wytr/KiCadCo2/Board2Pdf/temp/ESP8266_12F_BASIC-Edge_Cuts-colored.pdf

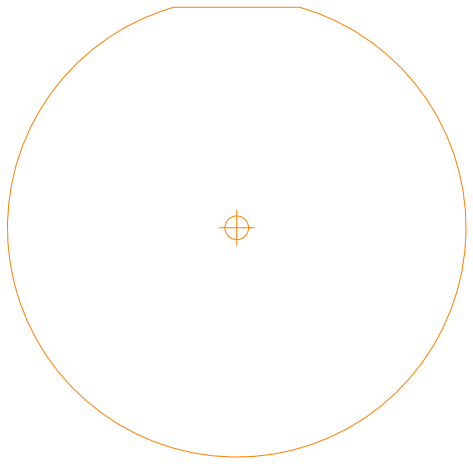
[picture p2: figure]
