wytr/KiCadCo2/Board2Pdf/temp/ESP8266_12F_BASIC-F_Silkscreen.pdf

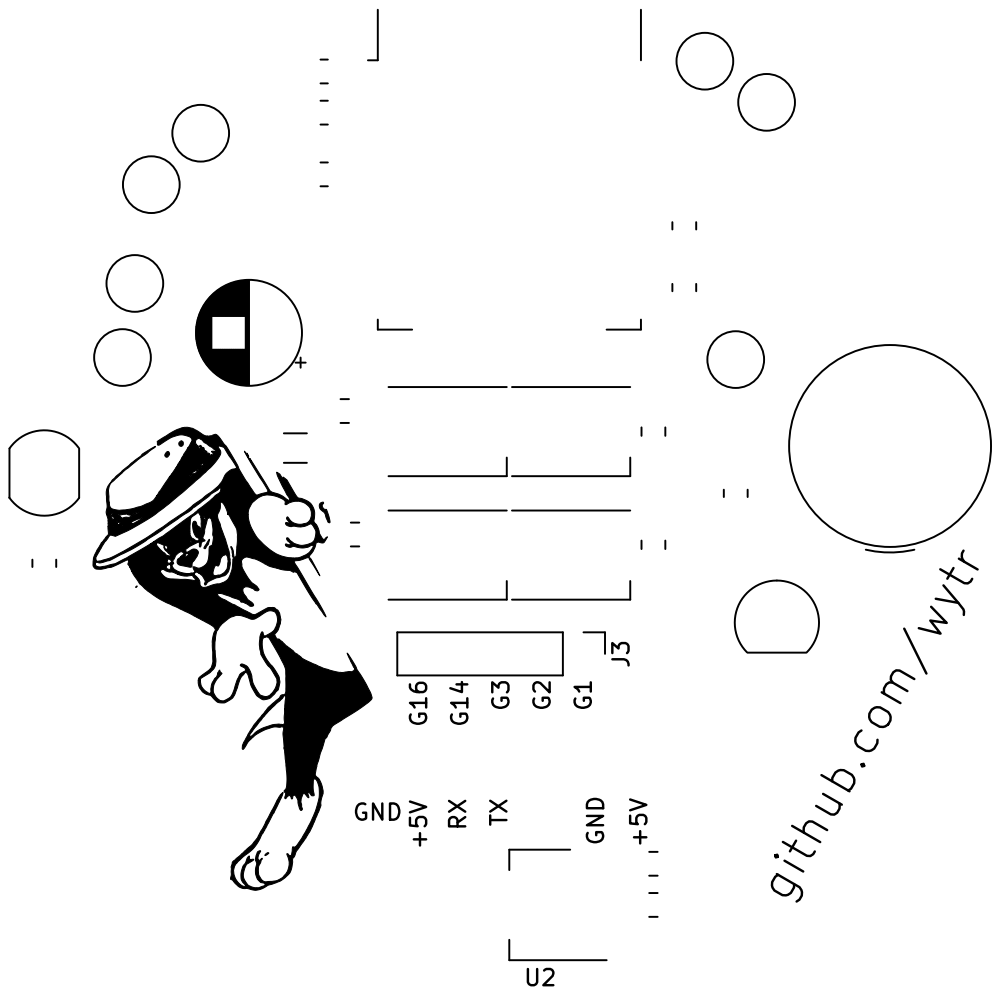
[picture p10: page 1]

G1 RXTX G3 G2 G14 GND github.com/wytr +5V G16 +5V GND
