wytr/KiCadCo2/Board2Pdf/temp/ESP8266_12F_BASIC-Edge_Cuts.pdf

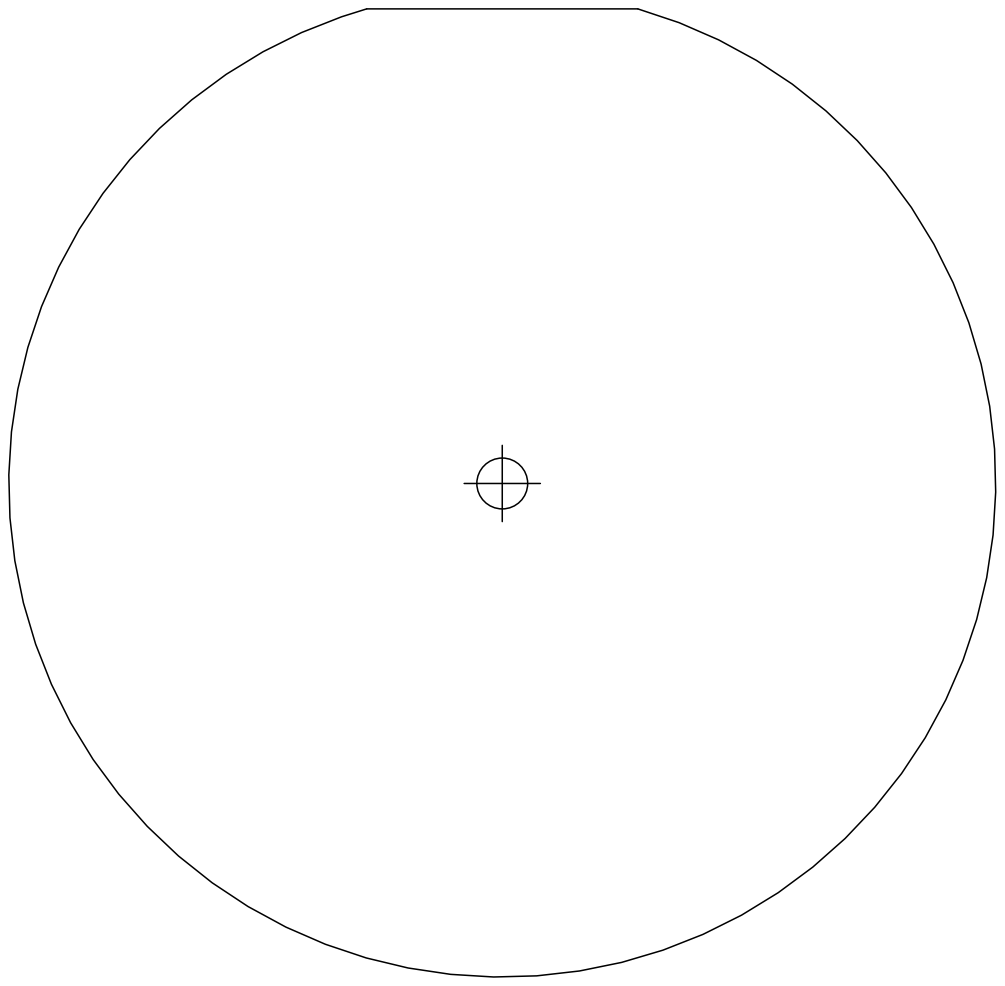
[picture p15: page 1]
