wytr/KiCadCo2/Board2Pdf/temp/ESP8266_12F_BASIC-F_Cu-colored.pdf

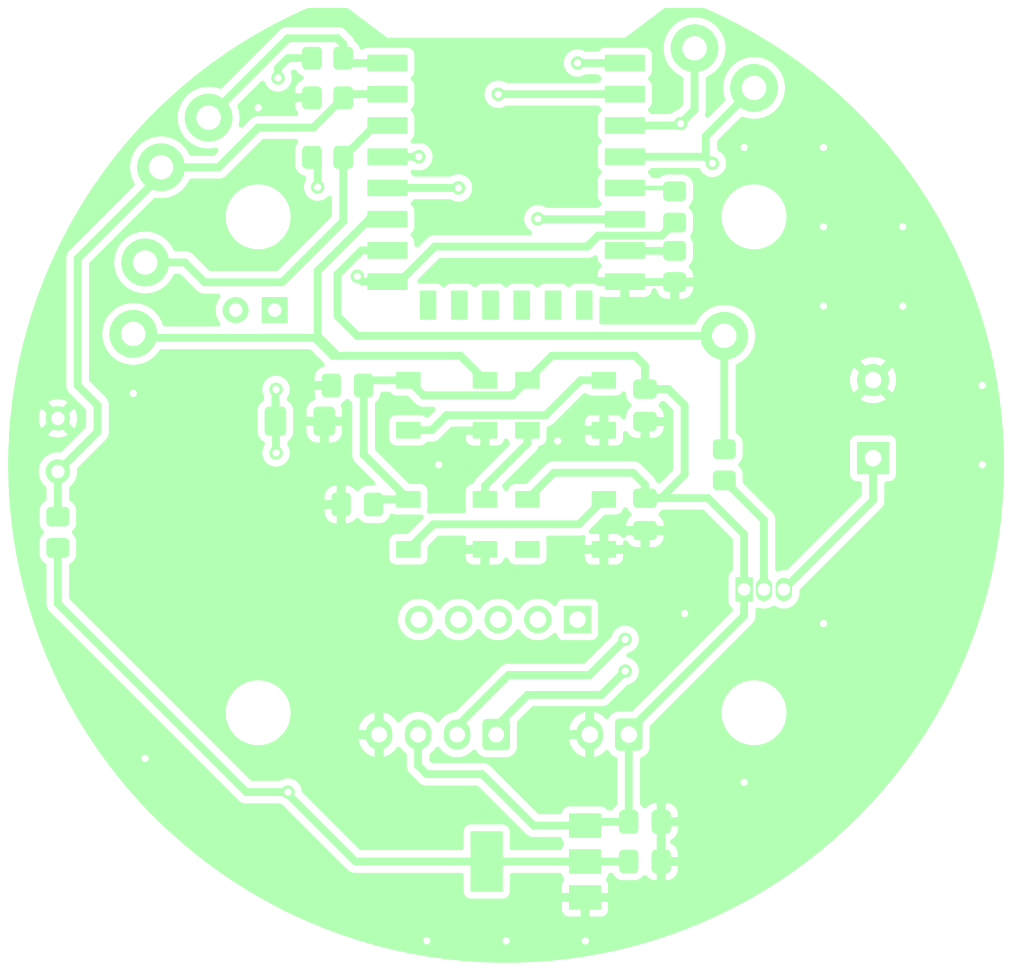
[picture p16: page 1]
