wytr/KiCadCo2/Board2Pdf/temp/ESP8266_12F_BASIC-F_Cu.pdf

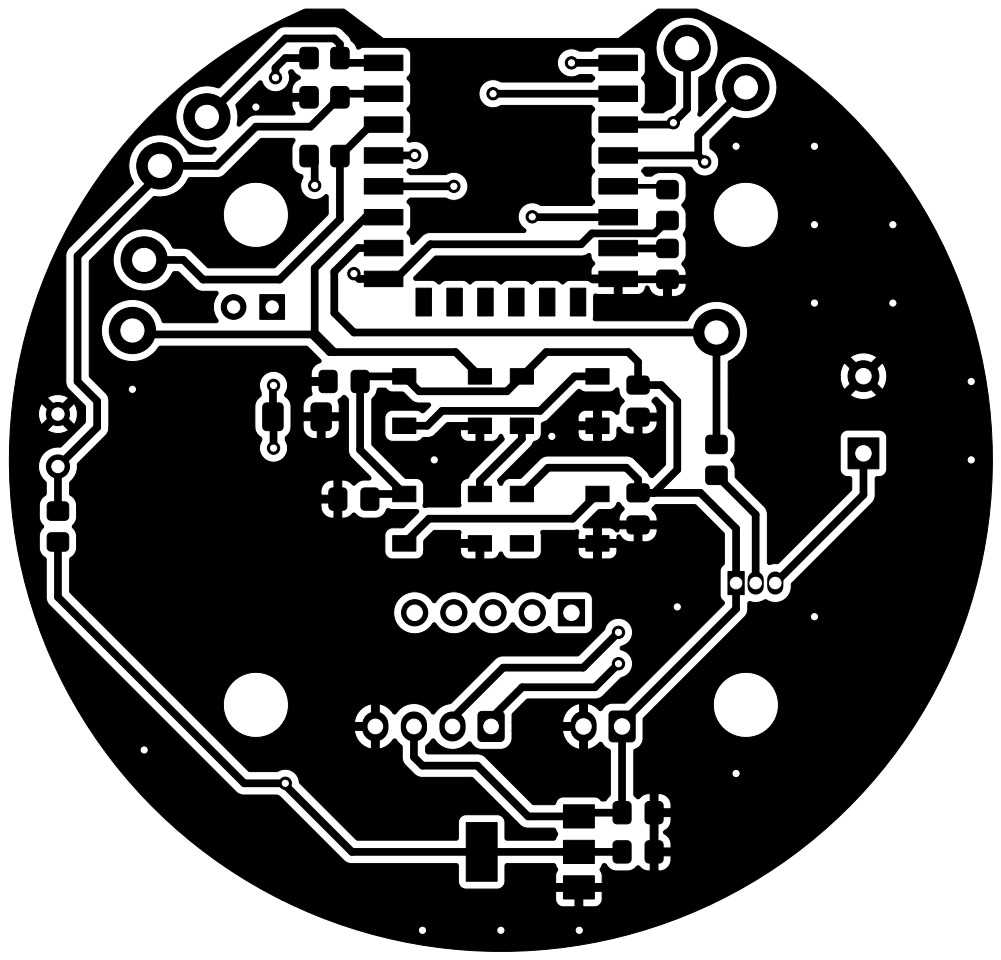
[picture p17: page 1]
