wytr/KiCadCo2/Board2Pdf/temp/ESP8266_12F_BASIC-F_Fab-colored.pdf

1 | 2 | 3 | 4 | 5 | 6

A

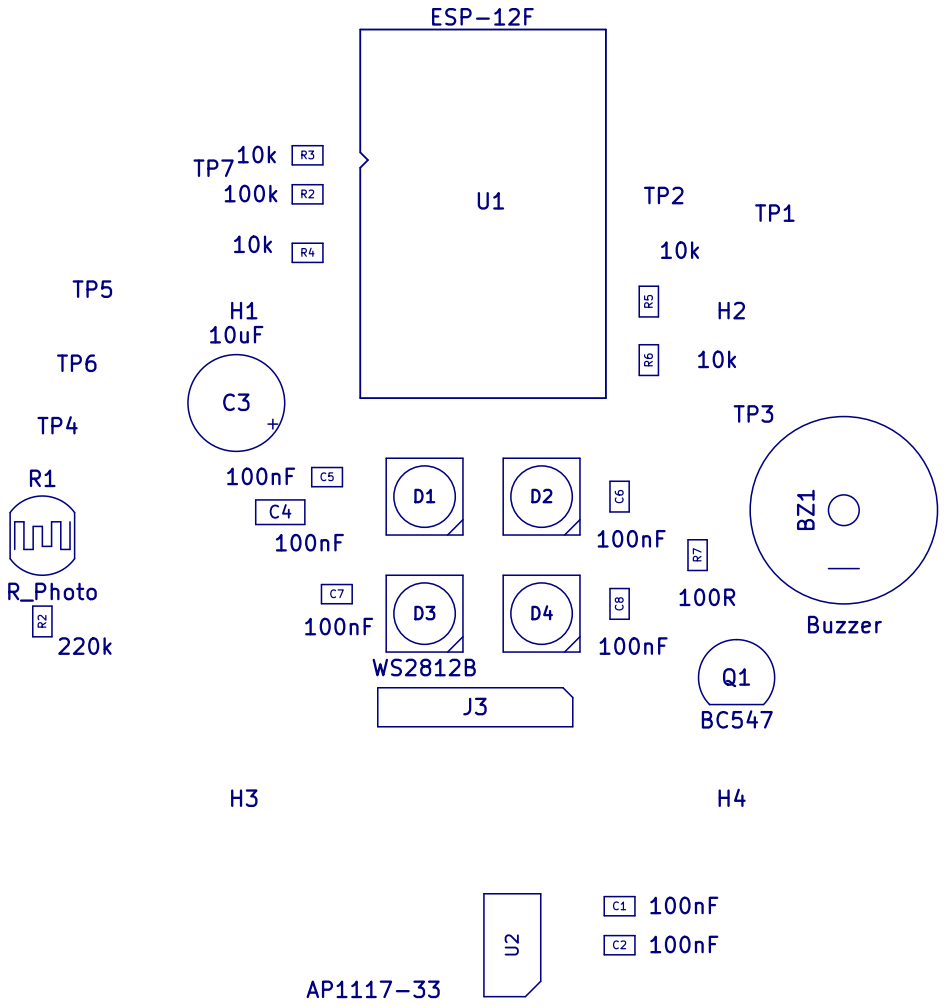
[picture p18: page 1]
