wytr/KiCadCo2/Board2Pdf/temp/ESP8266_12F_BASIC-F_Fab.pdf

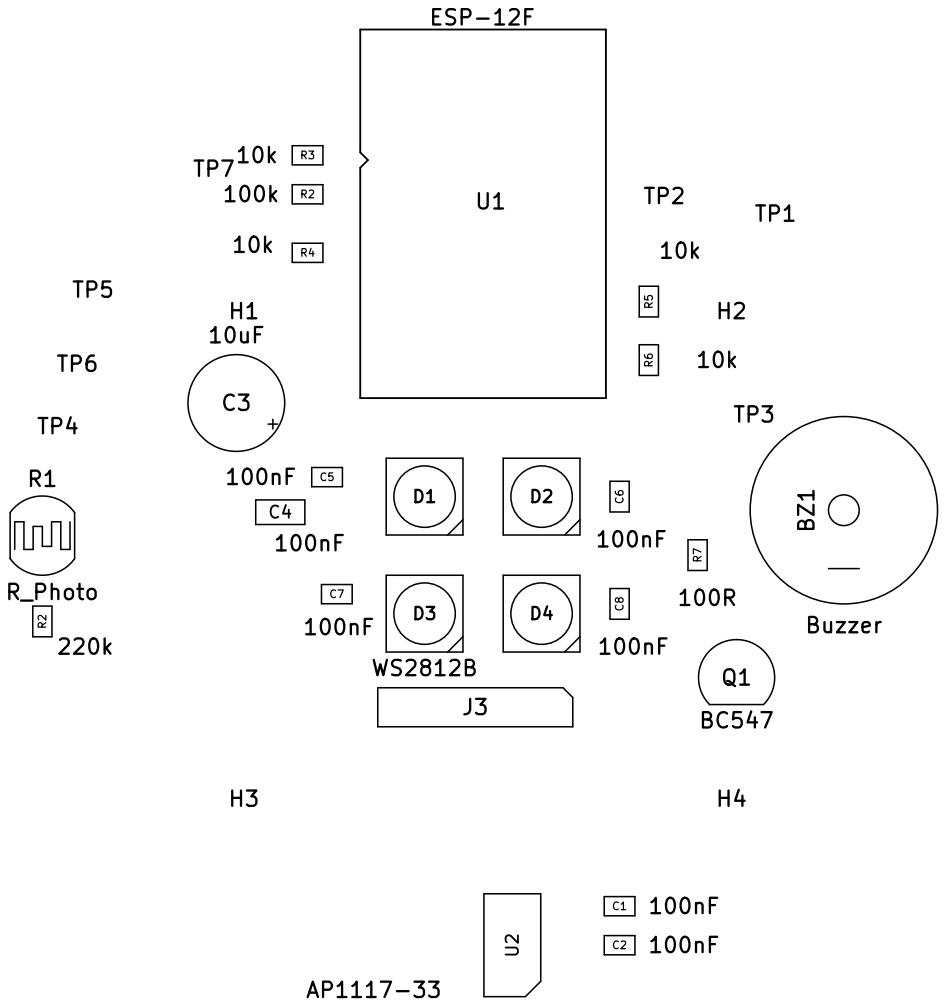
[picture p19: page 1]
