wytr/KiCadCo2/Board2Pdf/temp/ESP8266_12F_BASIC-F_Paste-colored.pdf

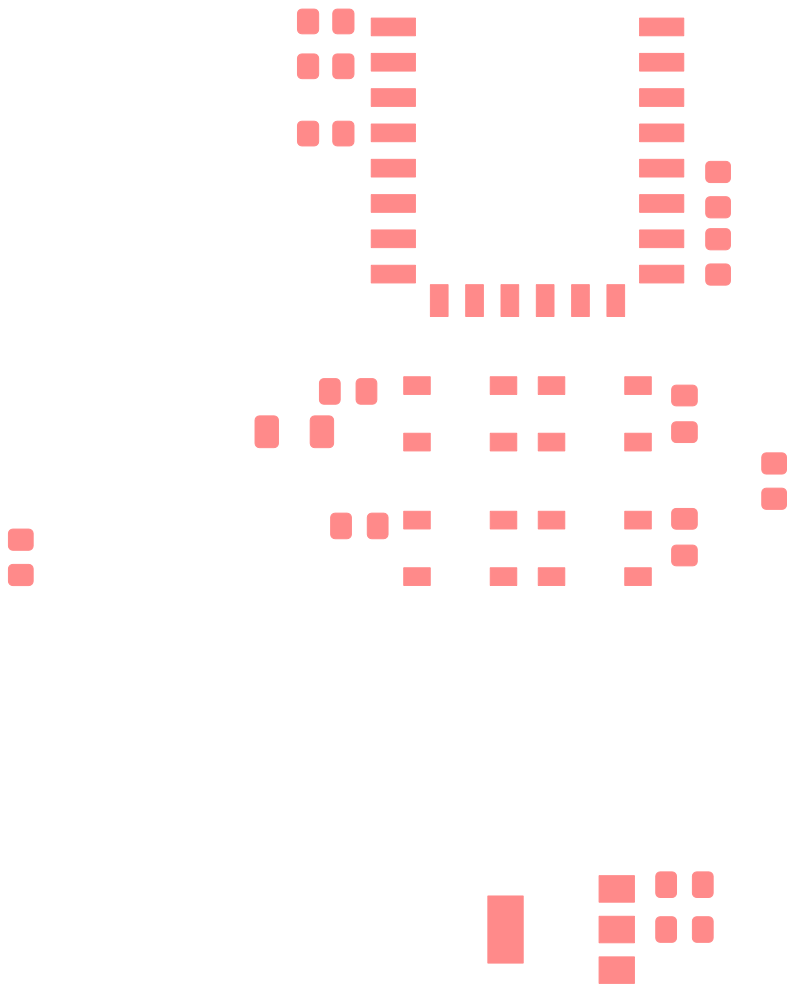
[picture p20: page 1]
