wytr/KiCadCo2/Board2Pdf/temp/ESP8266_12F_BASIC-F_Paste.pdf

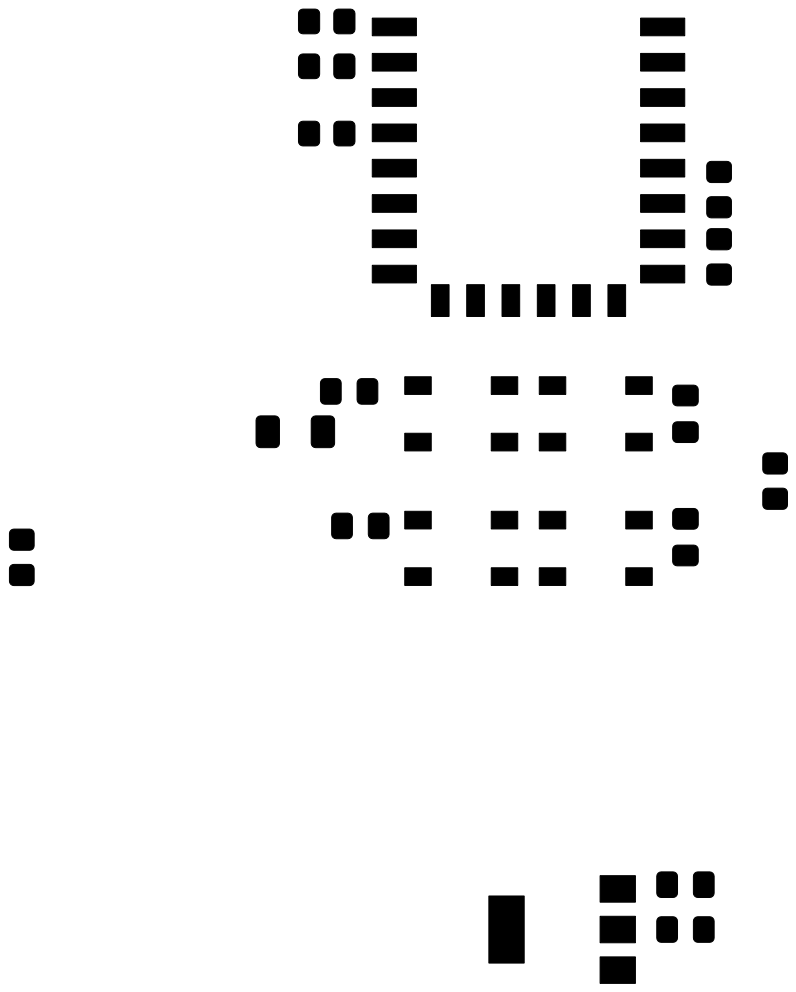
[picture p21: page 1]
